Aakee/BoomKah/hardware/kaboom.kicad_sch

## KiCad design hardware/kaboom.kicad_sch (2024-11-02)

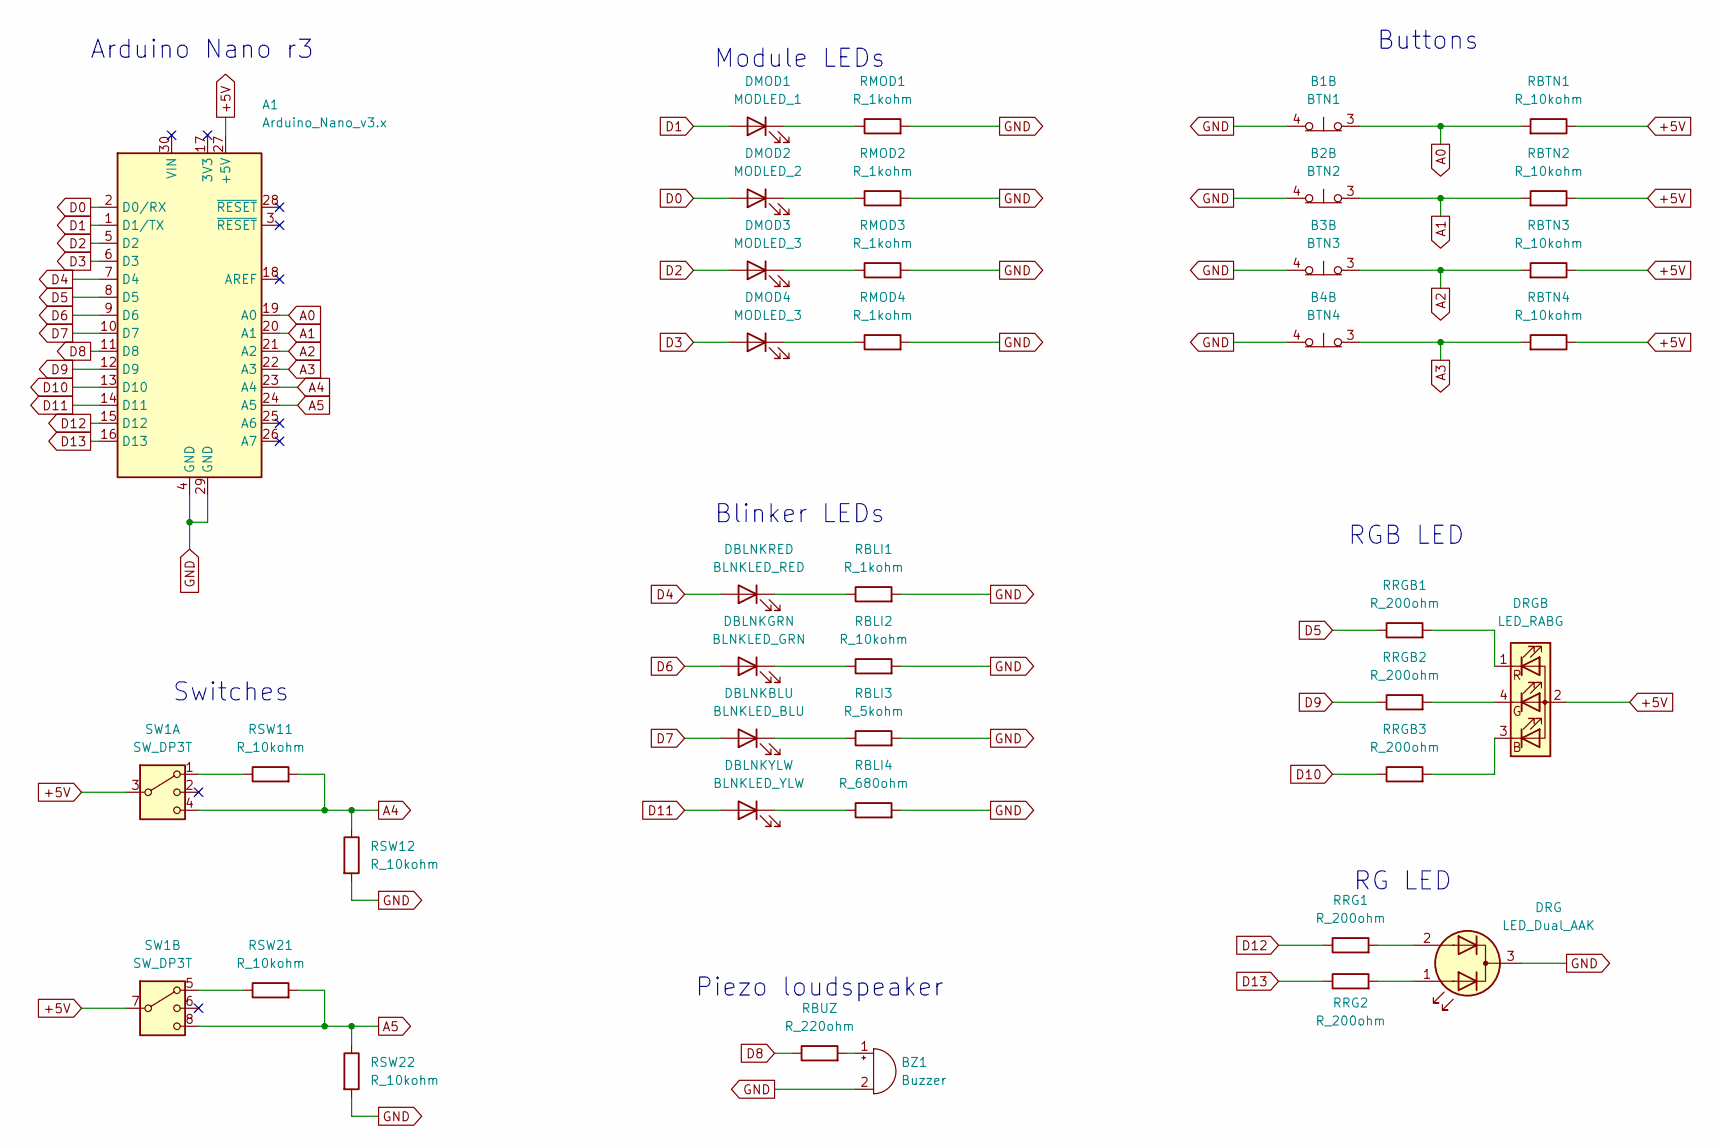
[picture p6: schematic kaboom.kicad_sch]

Parts:
A1: Arduino_Nano_v3.x; Arduino_Nano
B1: BTN1
B2: BTN2
B3: BTN3
B4: BTN4
BZ1: Buzzer
DBLNKBLU: BLNKLED_BLU
DBLNKGRN: BLNKLED_GRN
DBLNKRED: BLNKLED_RED
DBLNKYLW: BLNKLED_YLW
DMOD1: MODLED_1
DMOD2: MODLED_2
DMOD3, DMOD4: MODLED_3
DRG: LED_Dual_AAK
DRGB: LED_RABG
RBLI1: R_1kohm
RBLI2: R_10kohm
RBLI3: R_5kohm
RBLI4: R_680ohm
RBTN1, RBTN2, RBTN3, RBTN4: R_10kohm
RBUZ: R_220ohm
RMOD1, RMOD2, RMOD3, RMOD4: R_1kohm
RRG1, RRG2: R_200ohm
RRGB1, RRGB2, RRGB3: R_200ohm
RSW11, RSW12, RSW21, RSW22: R_10kohm
SW1: SW_DP3T

Connections:
+5V: A1.27 (+5V), DRGB.2 (A), RBTN1.1, RBTN2.1, RBTN3.1, RBTN4.1, SW1.3, SW1.7
A0: A1.19 (A0), B1.3 (1), RBTN1.2
A1: A1.20 (A1), B2.3 (1), RBTN2.2
A2: A1.21 (A2), B3.3 (1), RBTN3.2
A3: A1.22 (A3), B4.3 (1), RBTN4.2
A4: A1.23 (A4), RSW11.2, RSW12.1, SW1.4
A5: A1.24 (A5), RSW21.2, RSW22.1, SW1.8
D0: A1.2 (D0/RX), DMOD2.2 (A)
D1: A1.1 (D1/TX), DMOD1.2 (A)
D2: A1.5 (D2), DMOD3.2 (A)
D3: A1.6 (D3), DMOD4.2 (A)
D4: A1.7 (D4), DBLNKRED.2 (A)
D5: A1.8 (D5), RRGB1.1
D6: A1.9 (D6), DBLNKGRN.2 (A)
D7: A1.10 (D7), DBLNKBLU.2 (A)
D8: A1.11 (D8), RBUZ.1
D9: A1.12 (D9), RRGB2.1
D10: A1.13 (D10), RRGB3.1
D11: A1.14 (D11), DBLNKYLW.2 (A)
D12: A1.15 (D12), RRG1.1
D13: A1.16 (D13), RRG2.1
GND: A1.4 (GND), A1.29 (GND), B1.4 (2), B2.4 (2), B3.4 (2), B4.4 (2), BZ1.2 (-), DRG.3 (K), RBLI1.2, RBLI2.2, RBLI3.2, RBLI4.2, RMOD1.2, RMOD2.2, RMOD3.2, RMOD4.2, RSW12.2, RSW22.2
unnamed: BZ1.1 (+), RBUZ.2
unnamed: DBLNKBLU.1 (K), RBLI3.1
unnamed: DBLNKGRN.1 (K), RBLI2.1
unnamed: DBLNKRED.1 (K), RBLI1.1
unnamed: DBLNKYLW.1 (K), RBLI4.1
unnamed: DMOD1.1 (K), RMOD1.1
unnamed: DMOD2.1 (K), RMOD2.1
unnamed: DMOD3.1 (K), RMOD3.1
unnamed: DMOD4.1 (K), RMOD4.1
unnamed: DRG.1 (A1), RRG2.2
unnamed: DRG.2 (A2), RRG1.2
unnamed: DRGB.1 (RK), RRGB1.2
unnamed: DRGB.3 (BK), RRGB3.2
unnamed: DRGB.4 (GK), RRGB2.2
unnamed: RSW11.1, SW1.1
unnamed: RSW21.1, SW1.5

Notes on the sheet:
RGB LED
Blinker LEDs
RG LED
Arduino Nano r3
Buttons
Switches
Piezo loudspeaker
Module LEDs
