Aakee/BoomKah/src/main/module_led_handler.h

// Class to handle the module leds

#ifndef MODULE_LED_HANDLER
#define MODULE_LED_HANDLER

class ModuleLedHandler {

  public:

    // Creator and destructor
    ModuleLedHandler(int p1, int p2, int p3, int p4);
    ~ModuleLedHandler();

    // Set the given module LED on
    void set(int moduleNumber);

    // Turn off all module LEDs
    void off();


  private:

    // Pins of the module LEDs
    int pin1;
    int pin2;
    int pin3;
    int pin4;

};

#endif
